MrKohESP/Board/Hardware/Fab/Proofs/Image_20230208_231843.png

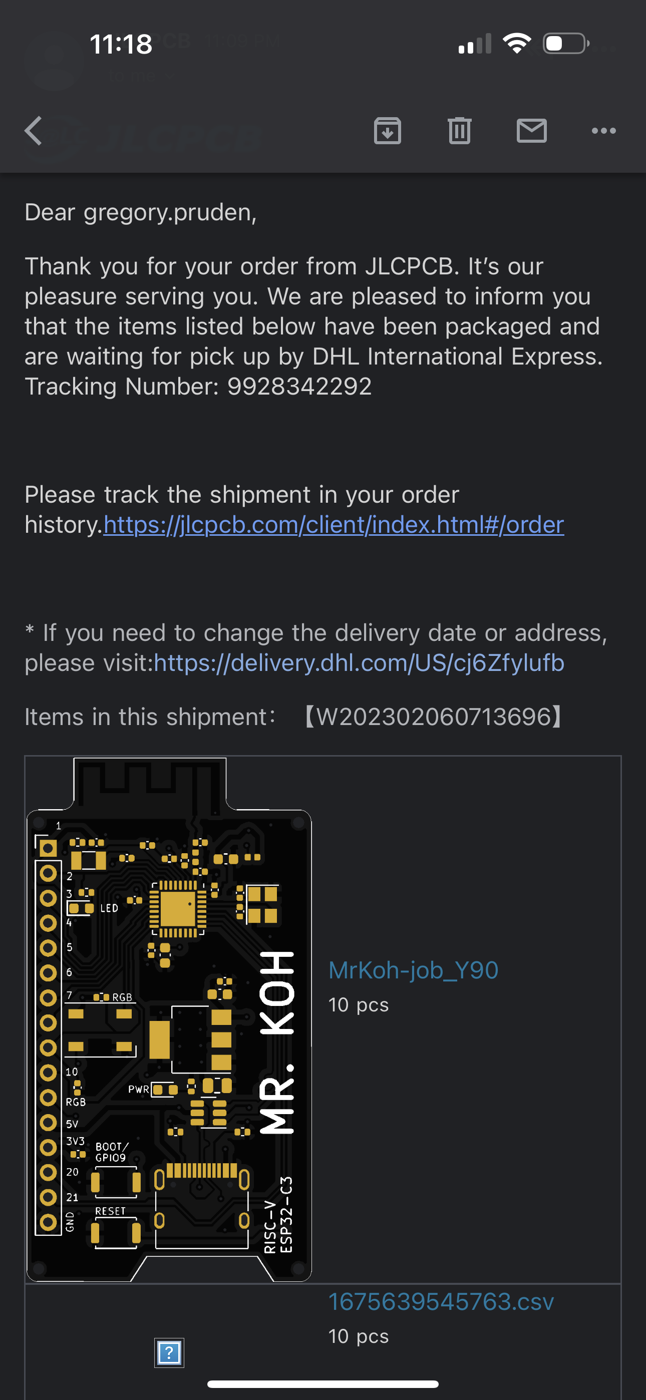
Hardware/Fab/Proofs/Image_20230208_231843.png
